flash62au/DccExController/actions.h

//
// DO NOT alter this file
// 

#define FUNCTION_NULL -1 // do nothing

#define FUNCTION_0 0 // lights
#define FUNCTION_1 1 // bell
#define FUNCTION_2 2 // horn
#define FUNCTION_3 3
#define FUNCTION_4 4
#define FUNCTION_5 5
#define FUNCTION_6 6
#define FUNCTION_7 7
#define FUNCTION_8 8
#define FUNCTION_9 9
#define FUNCTION_10 10
#define FUNCTION_11 11
#define FUNCTION_12 12
#define FUNCTION_13 13
#define FUNCTION_14 14
#define FUNCTION_15 15
#define FUNCTION_16 16
#define FUNCTION_17 17
#define FUNCTION_18 18
#define FUNCTION_19 19
#define FUNCTION_20 20
#define FUNCTION_21 21
#define FUNCTION_22 22
#define FUNCTION_23 23
#define FUNCTION_24 24
#define FUNCTION_25 25
#define FUNCTION_26 26
#define FUNCTION_27 27
#define FUNCTION_28 28
#define FUNCTION_29 29
#define FUNCTION_30 30
#define FUNCTION_31 31

#define SPEED_STOP 30
#define SPEED_UP 31
#define SPEED_DOWN 32
#define SPEED_UP_FAST 33
#define SPEED_DOWN_FAST 34
#define E_STOP 35
#define SPEED_MULTIPLIER 36

#define POWER_TOGGLE 40
#define POWER_ON 41
#define POWER_OFF 42

#define DIRECTION_TOGGLE 50
#define DIRECTION_FORWARD 51
#define DIRECTION_REVERSE 52

#define NEXT_THROTTLE 53

#define SPEED_STOP_THEN_TOGGLE_DIRECTION 54   // stops the loco if moving.  Toggles the direction if stationary.

#define E_STOP_CURRENT_LOCO 55

#define MAX_THROTTLE_INCREASE 56
#define MAX_THROTTLE_DECREASE 57

#define REQUEST_SERVER_INFO 58

#define CUSTOM_1 121
#define CUSTOM_2 122
#define CUSTOM_3 123
#define CUSTOM_4 124
#define CUSTOM_5 125
#define CUSTOM_6 126
#define CUSTOM_7 127

#define SHOW_HIDE_BATTERY 504   // the battery test must be enabled for this to have any effect
